Nara-On/MsCatch-ME/diagrams/DiagramaAS.png

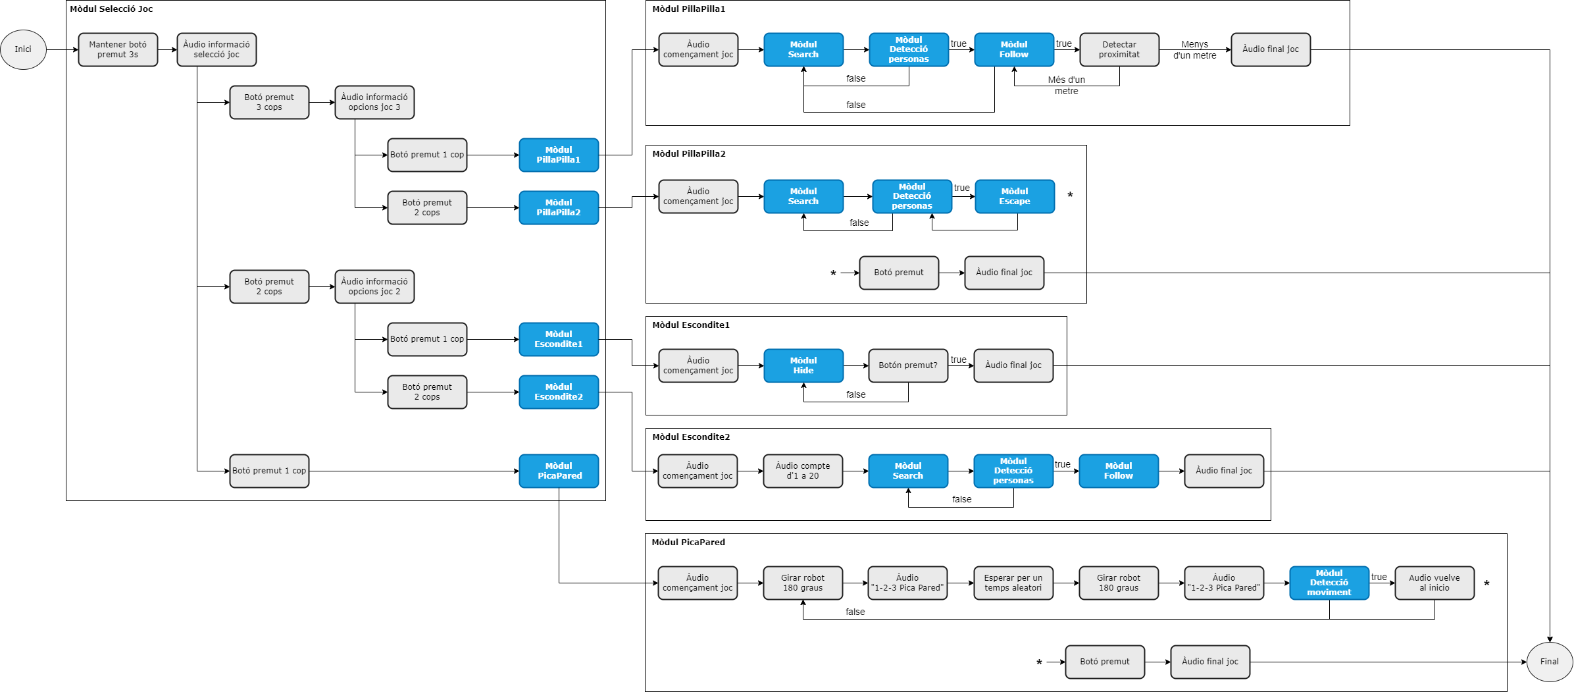
diagrams/DiagramaAS.png
