Nara-On/MsCatch-ME/diagrams/DiagramaAS_versioPresentacio.png

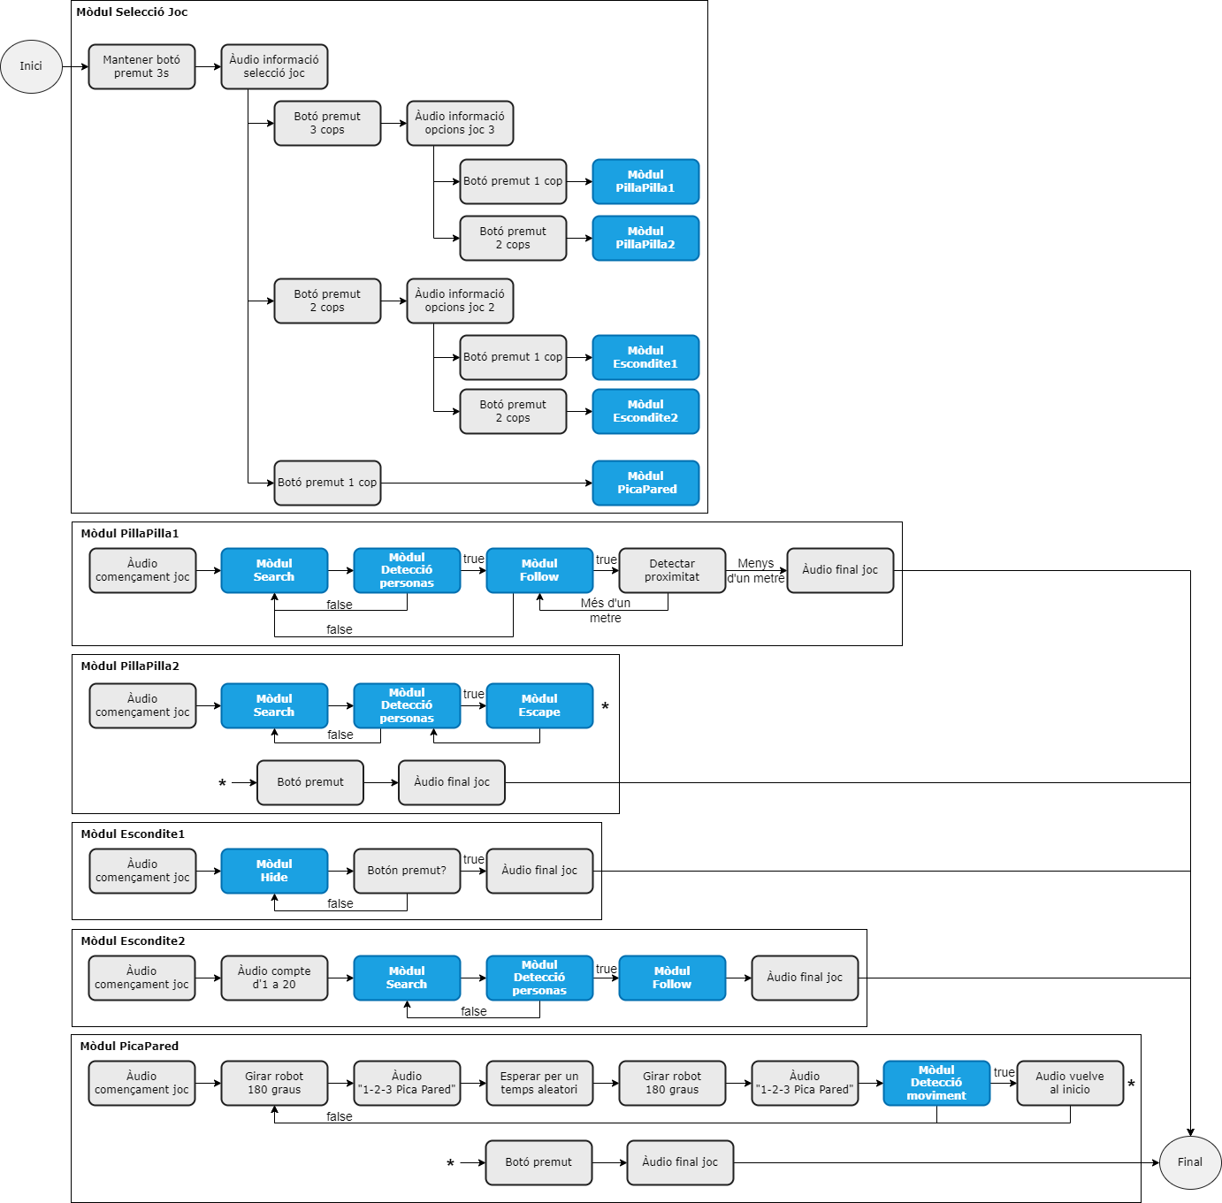
diagrams/DiagramaAS_versioPresentacio.png
