Nara-On/MsCatch-ME/diagrams/DiagramaModulPicaPared.png

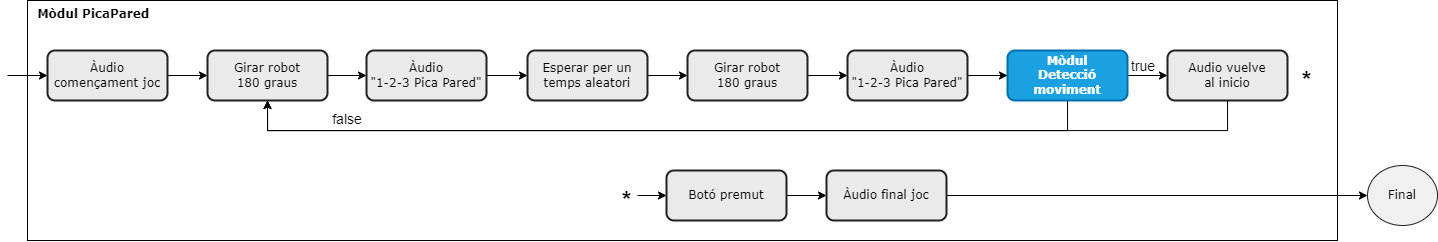
diagrams/DiagramaModulPicaPared.png
