Nara-On/MsCatch-ME/diagrams/DiagramaModulSeleccioJoc.png

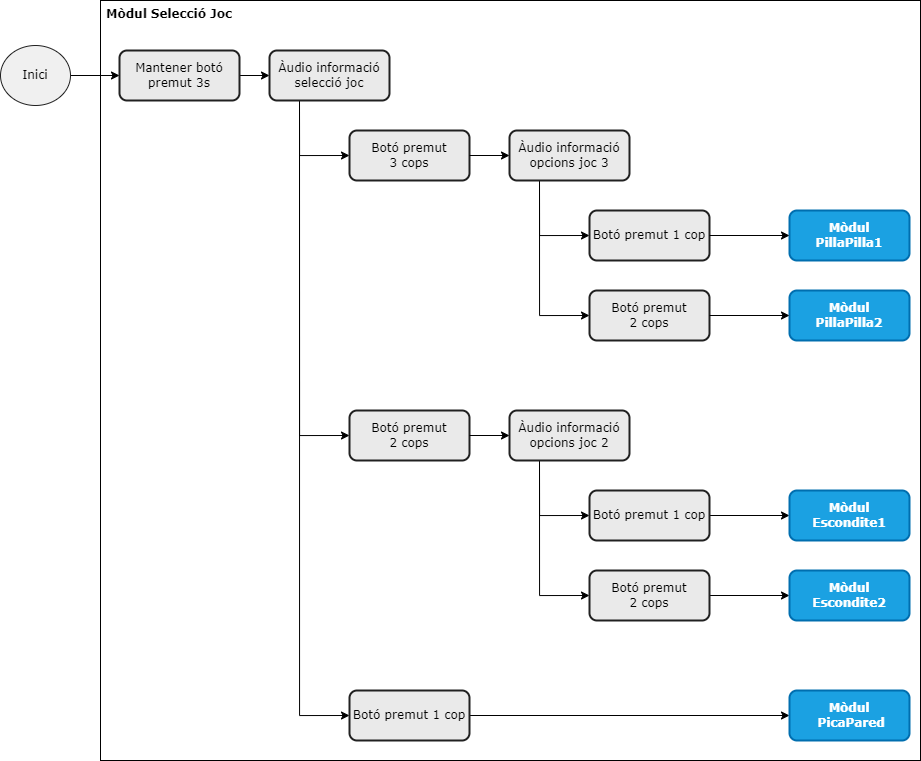
diagrams/DiagramaModulSeleccioJoc.png
