Nara-On/MsCatch-ME/diagrams/DiagramaModulsEscondite.png

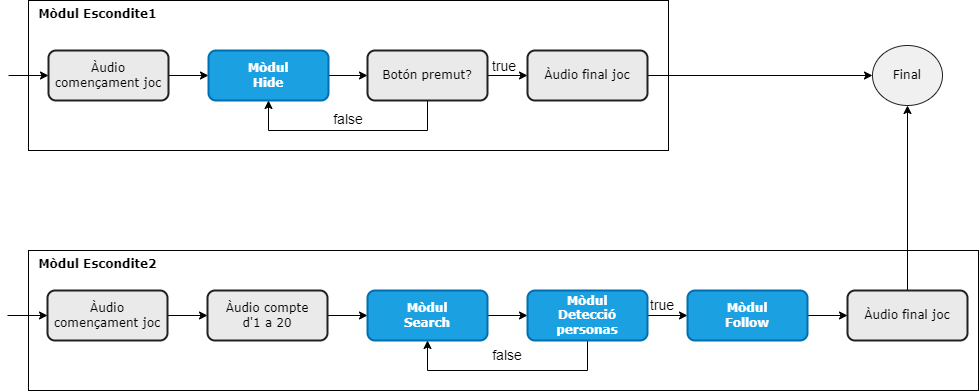
diagrams/DiagramaModulsEscondite.png
