Nara-On/MsCatch-ME/diagrams/DiagramaModulsPillaPilla.png

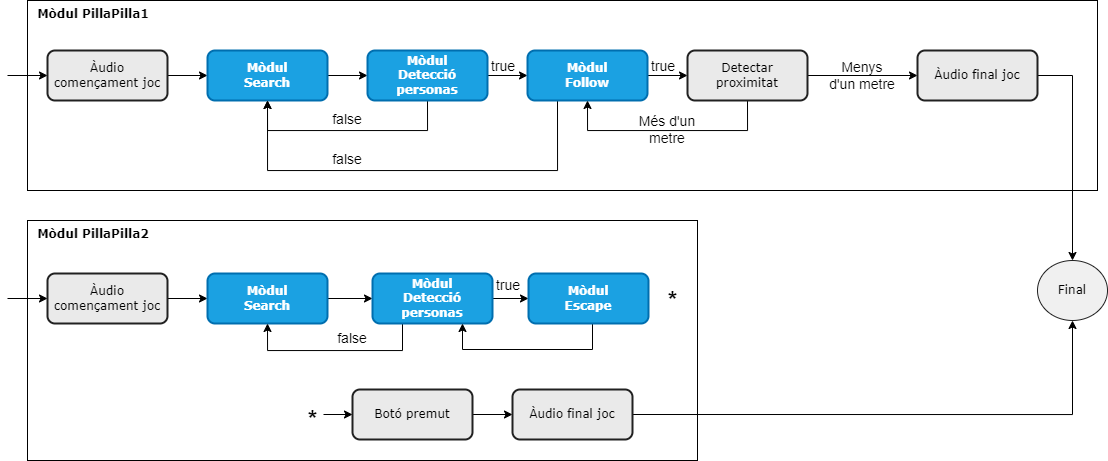
diagrams/DiagramaModulsPillaPilla.png
