Nara-On/MsCatch-ME/diagrams/EsquemaHW.jpg

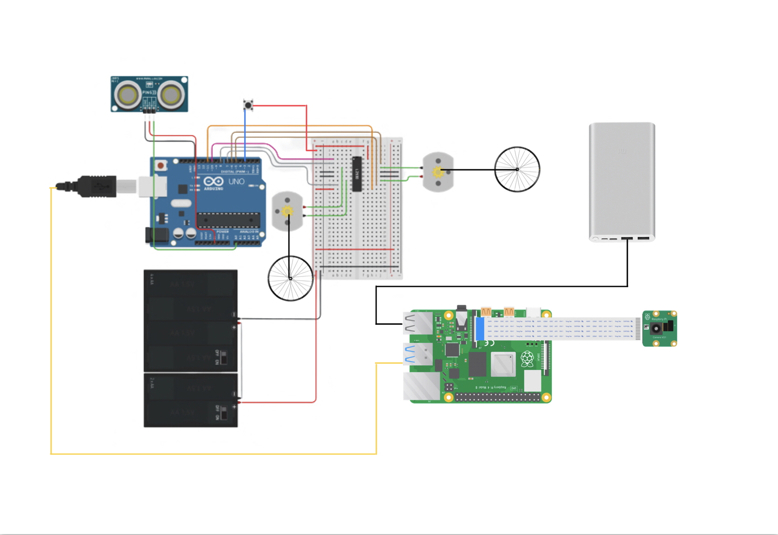
diagrams/EsquemaHW.jpg
