Nara-On/MsCatch-ME/documentation/images/photoMsCatchME_1.jpg

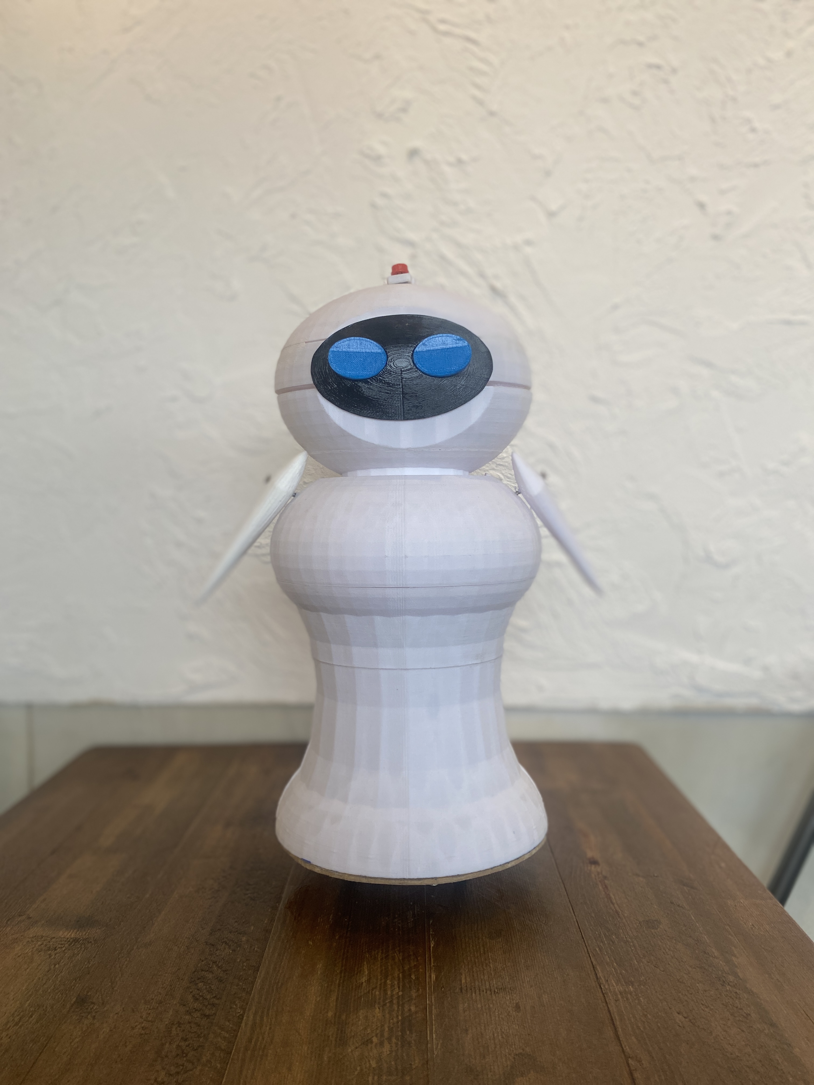
documentation/images/photoMsCatchME_1.jpg
