Nara-On/MsCatch-ME/documentation/images/photoMsCatchME_5.JPG

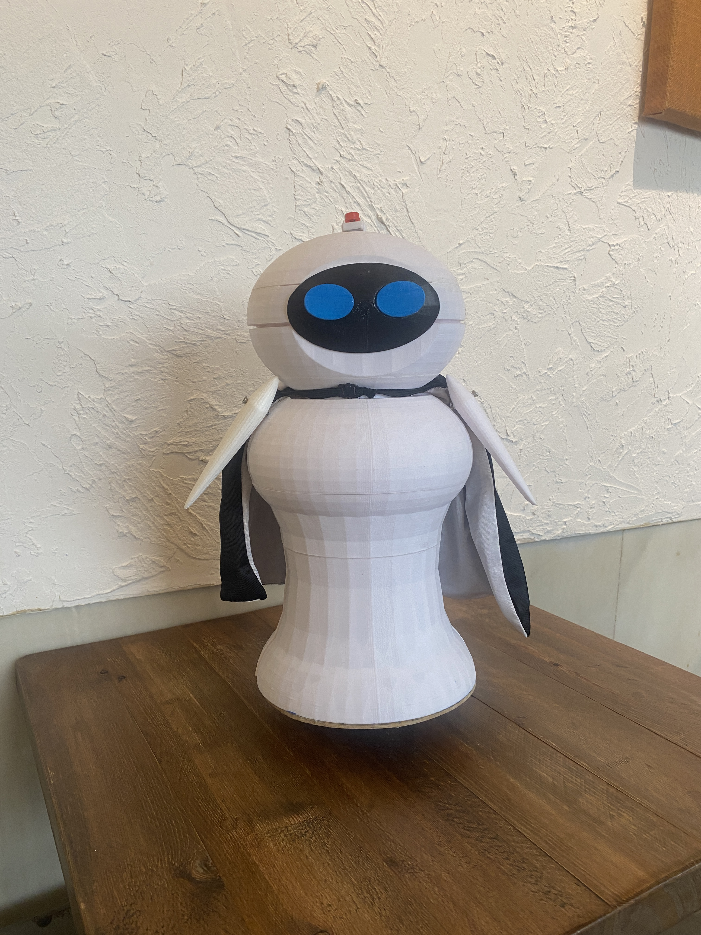
documentation/images/photoMsCatchME_5.JPG
