Nara-On/MsCatch-ME/documentation/images/photoMsCatchME_6.JPG

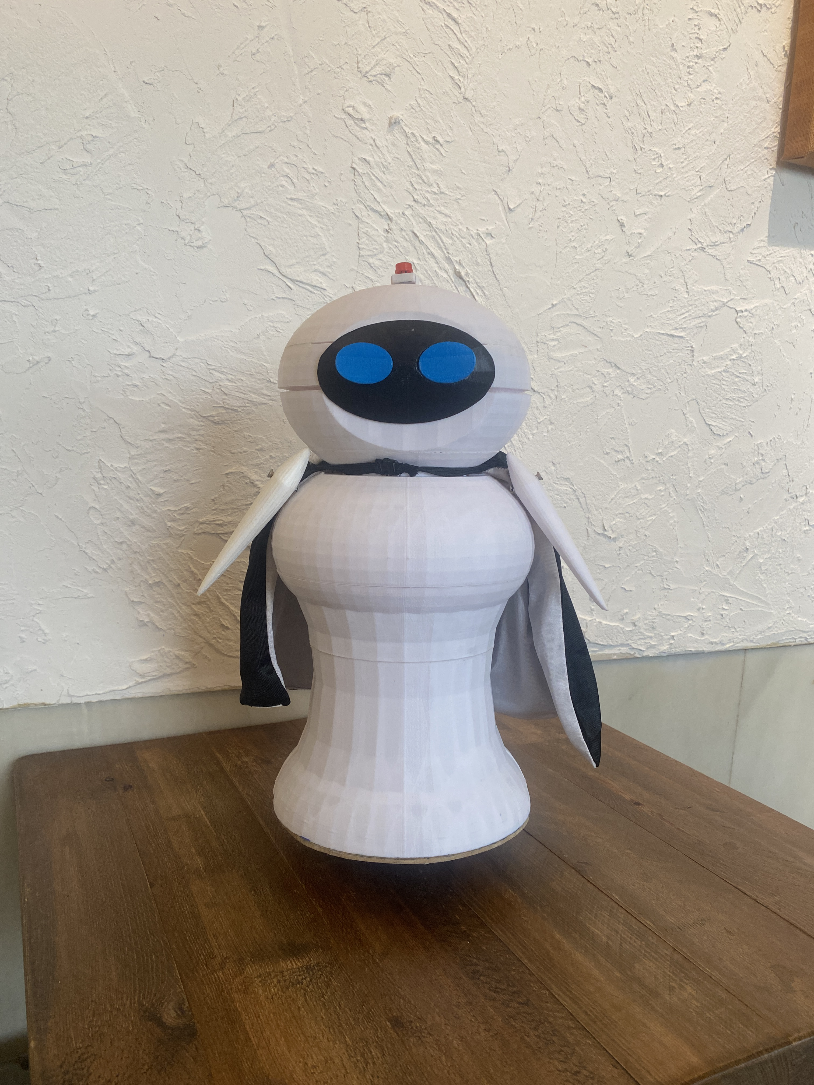
documentation/images/photoMsCatchME_6.JPG
