Nara-On/MsCatch-ME/documentation/images/photoMsCatchME_8.JPG

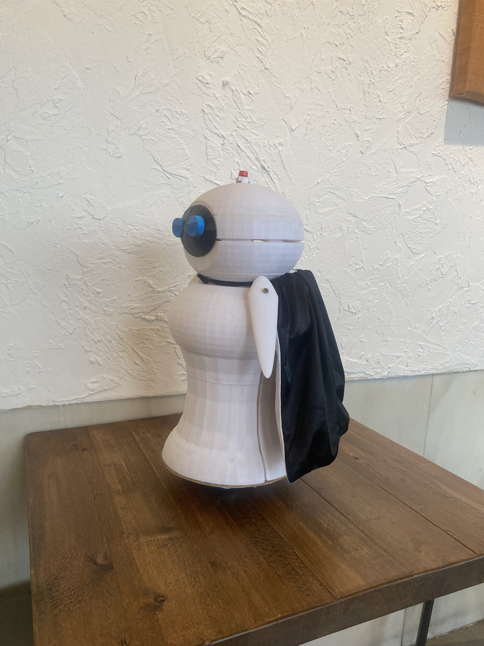
documentation/images/photoMsCatchME_8.JPG
