Nara-On/MsCatch-ME/documentation/images/photoMsCatchME_9.JPG

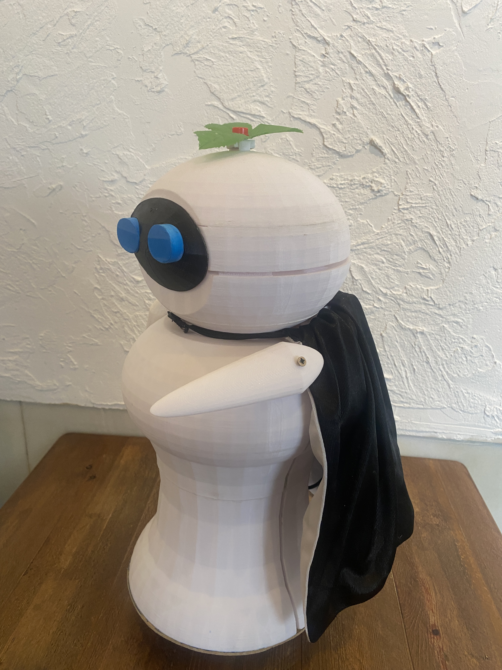
documentation/images/photoMsCatchME_9.JPG
