Nara-On/MsCatch-ME/documentation/images/photoMsCatchME_13.JPG

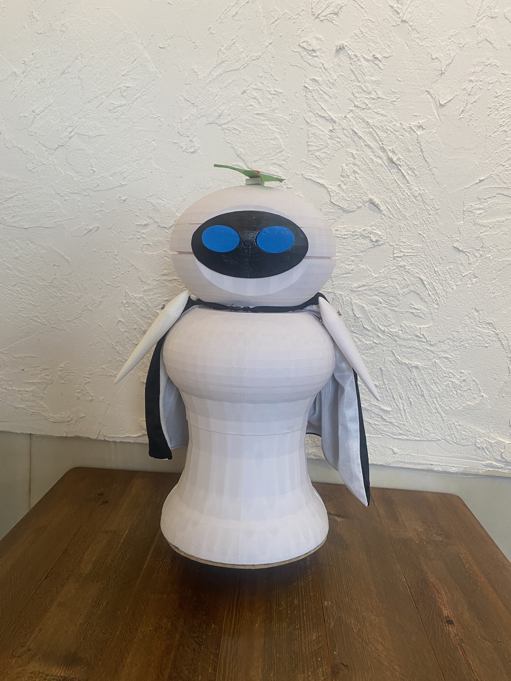
documentation/images/photoMsCatchME_13.JPG
