Nara-On/MsCatch-ME/documentation/images/photoMsCatchME_14.JPG

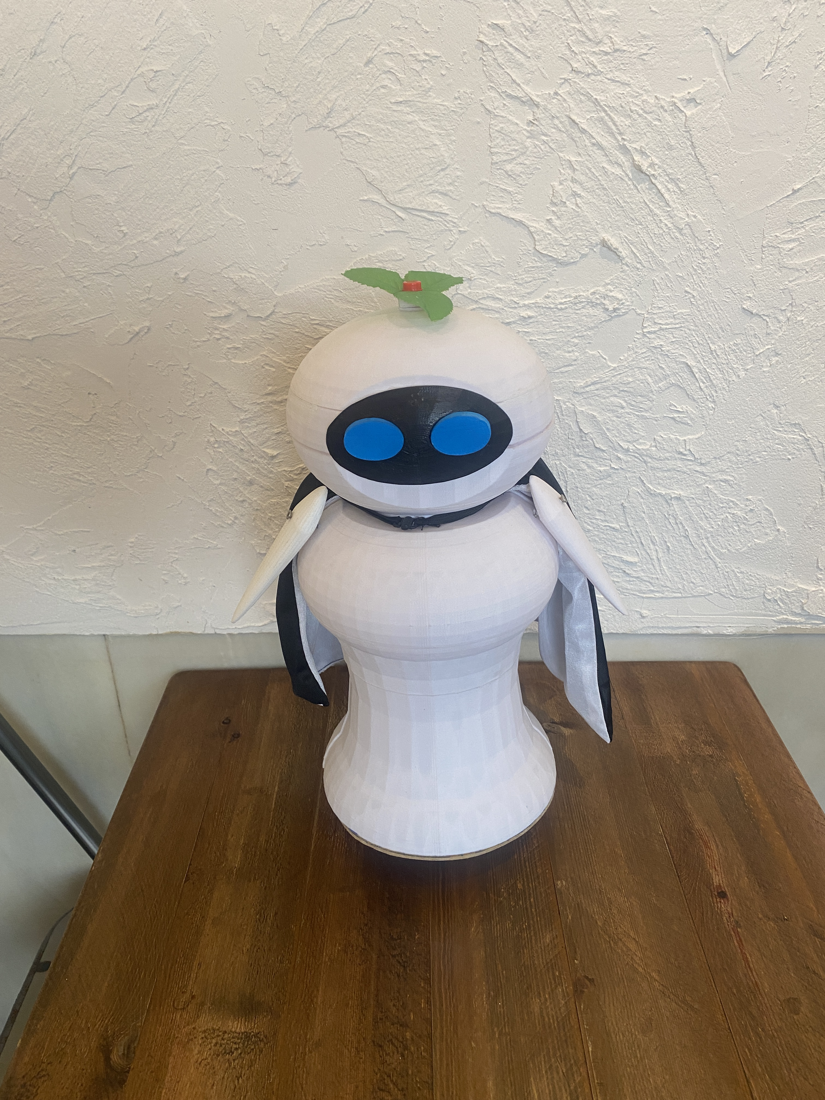
documentation/images/photoMsCatchME_14.JPG
